whowechina/diva_pico/Production/CAD/diva_pico_base.stl

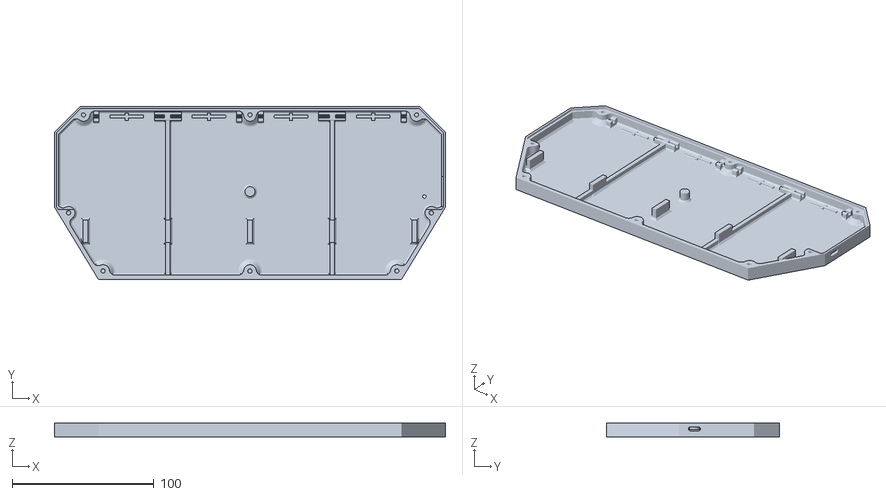
[picture p27: CAD file, 2025-04-21]
Production/CAD/diva_pico_base.stl
276.0 x 122.0 x 10.0
