whowechina/diva_pico/PCB/plus/3dmodels/SW_Kailh_Choc_V1.stp

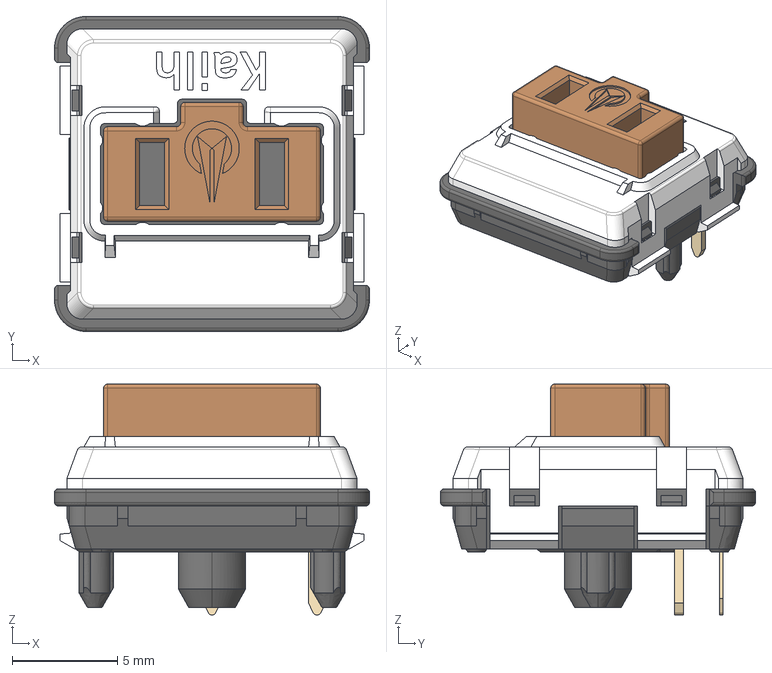
[picture p28: CAD file, 2023-12-16]
PCB/plus/3dmodels/SW_Kailh_Choc_V1.stp
15.0 x 15.0 x 11.0 mm
