whowechina/diva_pico/PCB/plus/3dmodels/WS2812B.step

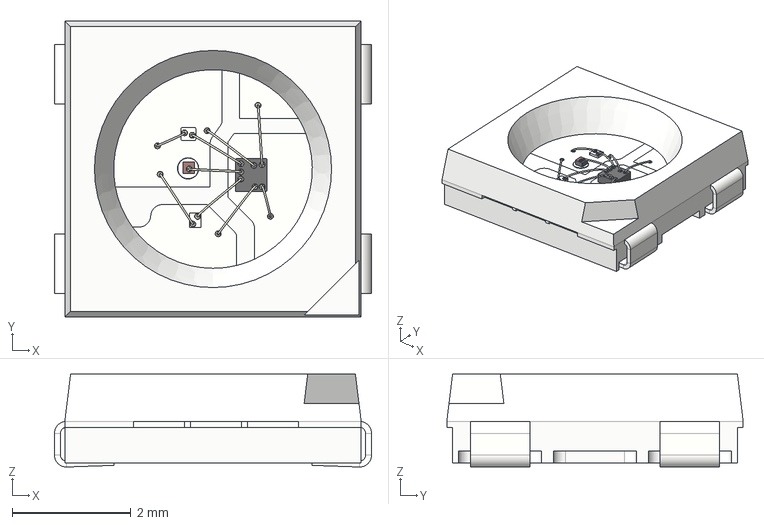
[picture p29: CAD file, 2023-12-16]
PCB/plus/3dmodels/WS2812B.step
5.35 x 5.00 x 1.57 mm
