whowechina/diva_pico/PCB/plus/3dmodels/chu_keypad_lgp.step

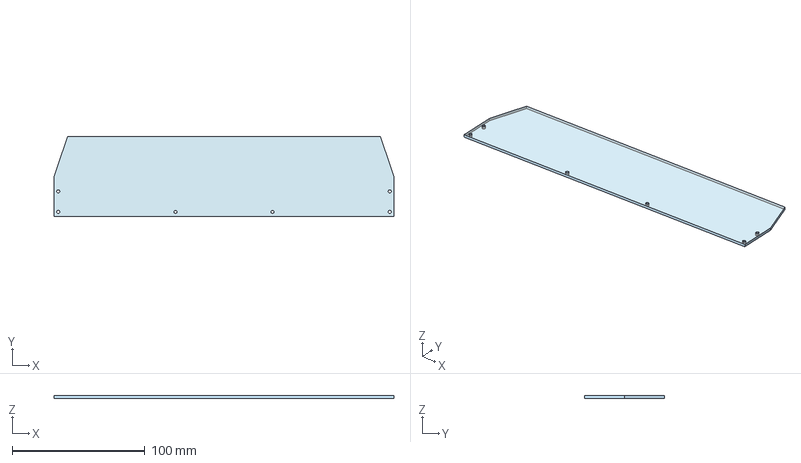
[picture p31: CAD file, 2023-12-16]
PCB/plus/3dmodels/chu_keypad_lgp.step
256.0 x 60.0 x 2.00 mm
