whowechina/diva_pico/PCB/plus/3dmodels/WS2812-2020.STEP

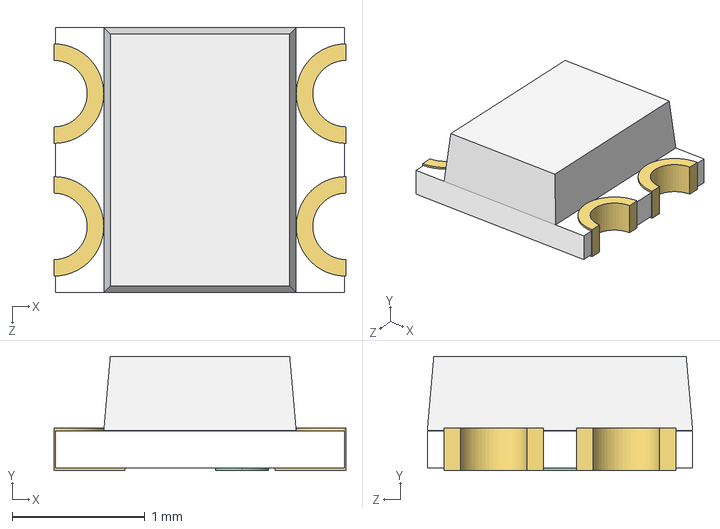
[picture p32: CAD file, 2023-12-16]
PCB/plus/3dmodels/WS2812-2020.STEP
2.20 x 0.86 x 2.00 mm
