whowechina/diva_pico/PCB/plus/3dmodels/J 2835.step

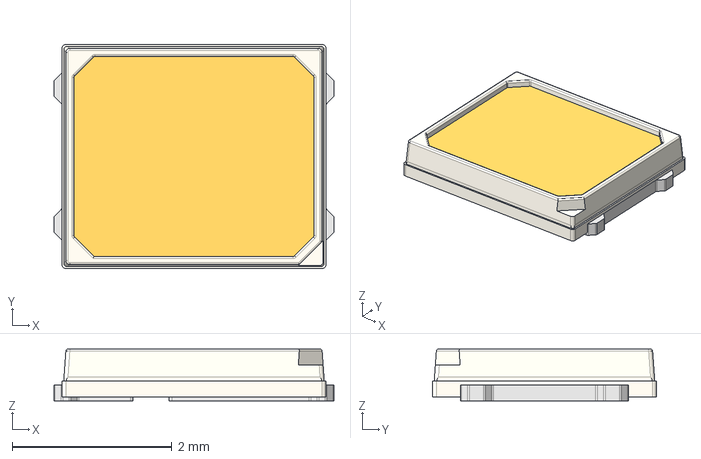
[picture p33: CAD file, 2023-12-16]
PCB/plus/3dmodels/J 2835.step
3.50 x 2.80 x 0.65 mm
