whowechina/diva_pico/PCB/plus/3dmodels/WS2812-0807.STEP

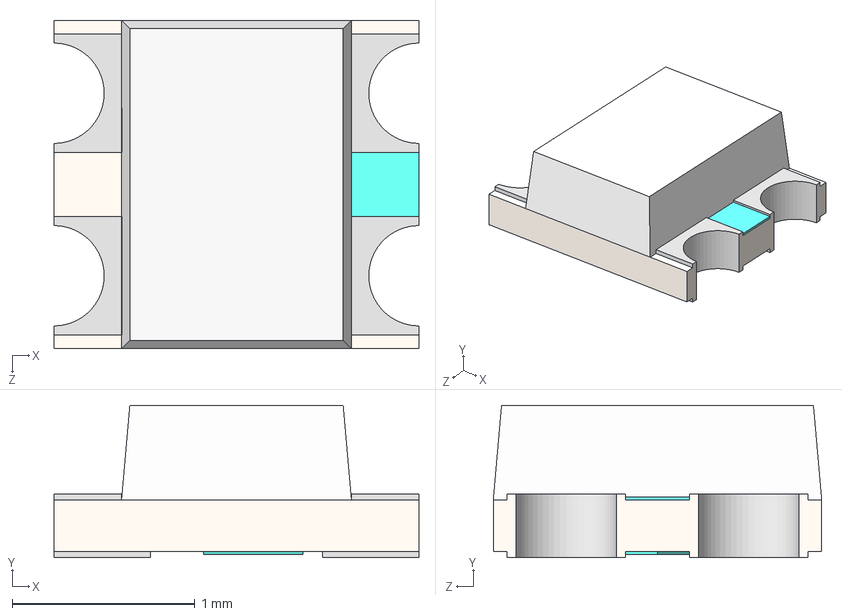
[picture p34: CAD file, 2023-12-16]
PCB/plus/3dmodels/WS2812-0807.STEP
2.00 x 0.835 x 1.80 mm
