whowechina/diva_pico/PCB/plus/3dmodels/Kailh LP Choc PC Keycap.step

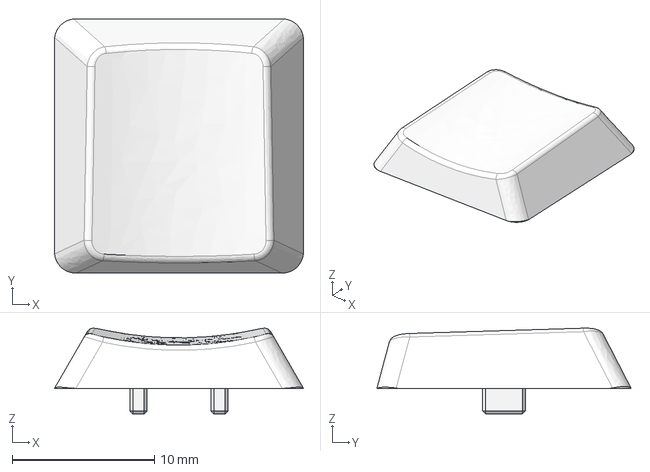
[picture p35: CAD file, 2023-12-16]
PCB/plus/3dmodels/Kailh LP Choc PC Keycap.step
17.5 x 17.9 x 6.03 mm
