whowechina/diva_pico/PCB/plus/3dmodels/SW_Hotswap_Kailh_MX.stp

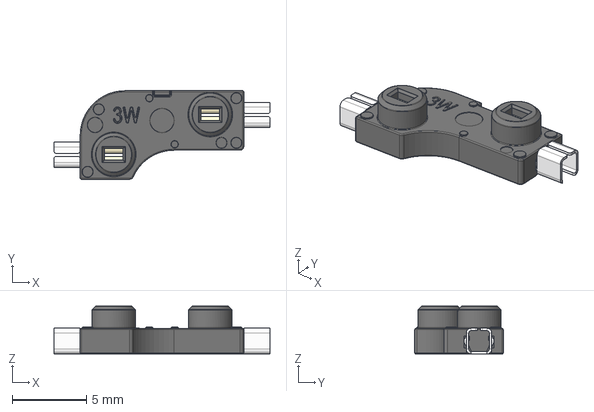
[picture p36: CAD file, 2023-12-16]
PCB/plus/3dmodels/SW_Hotswap_Kailh_MX.stp
14.5 x 5.95 x 3.22 mm
