whowechina/diva_pico/PCB/plus/3dmodels/SKPMAM.STEP

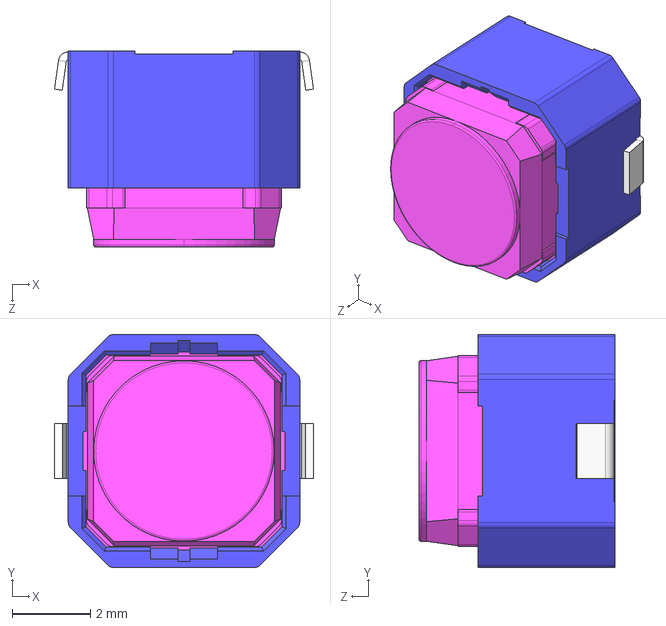
[picture p37: CAD file, 2023-12-16]
PCB/plus/3dmodels/SKPMAM.STEP
6.60 x 5.94 x 5.00 mm
