whowechina/diva_pico/PCB/plus/3dmodels/gp2y0e03.3mf

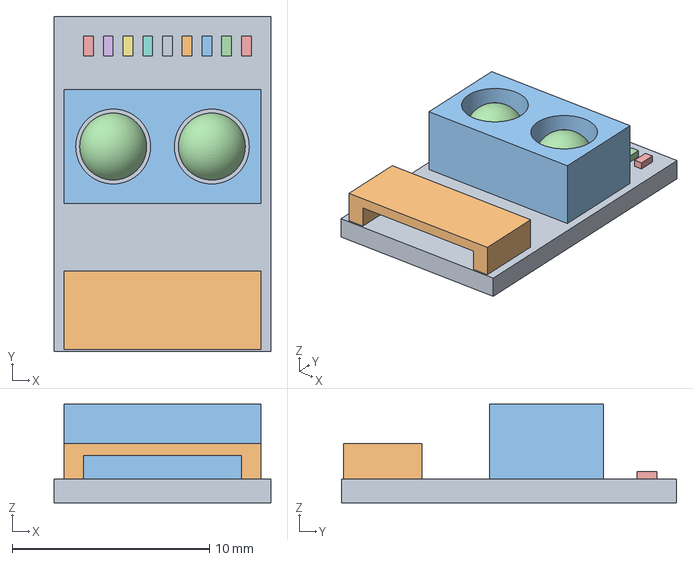
[picture p38: CAD file, 2023-12-16]
PCB/plus/3dmodels/gp2y0e03.3mf
11.0 x 17.0 x 5.00 mm
