whowechina/diva_pico/PCB/plus/3dmodels/Magnetic Pogo Connector 5 Pin (F).STEP

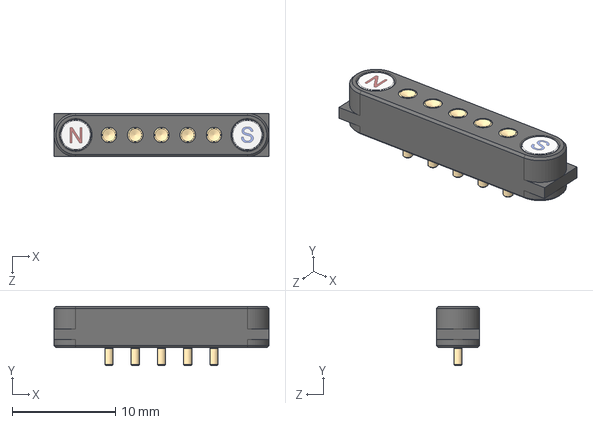
[picture p39: CAD file, 2023-12-16]
PCB/plus/3dmodels/Magnetic Pogo Connector 5 Pin (F).STEP
20.8 x 5.75 x 4.20 mm
