whowechina/diva_pico/PCB/plus/3dmodels/Tact Switch 4.5mm SMT.step

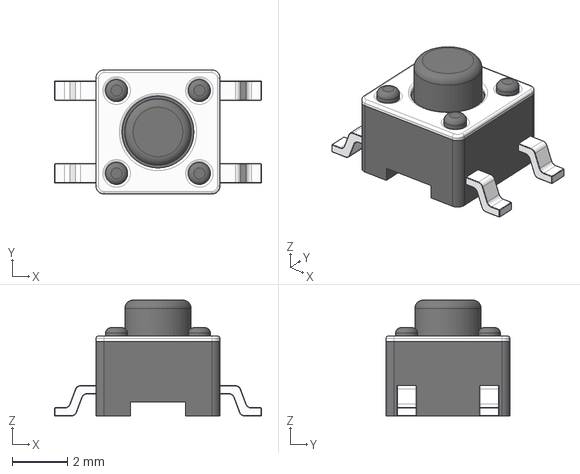
[picture p40: CAD file, 2023-12-16]
PCB/plus/3dmodels/Tact Switch 4.5mm SMT.step
7.50 x 4.50 x 4.20 mm
