whowechina/diva_pico/PCB/plus/3dmodels/User Library-WS2812-2020.step

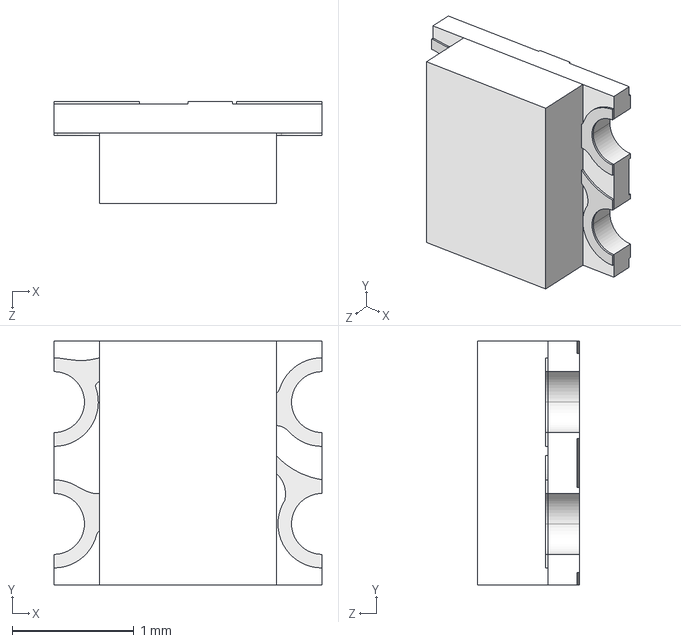
[picture p41: CAD file, 2023-12-16]
PCB/plus/3dmodels/User Library-WS2812-2020.step
2.20 x 2.00 x 0.84 mm
