whowechina/diva_pico/PCB/plus/3dmodels/EVQ-P1D05M.stp

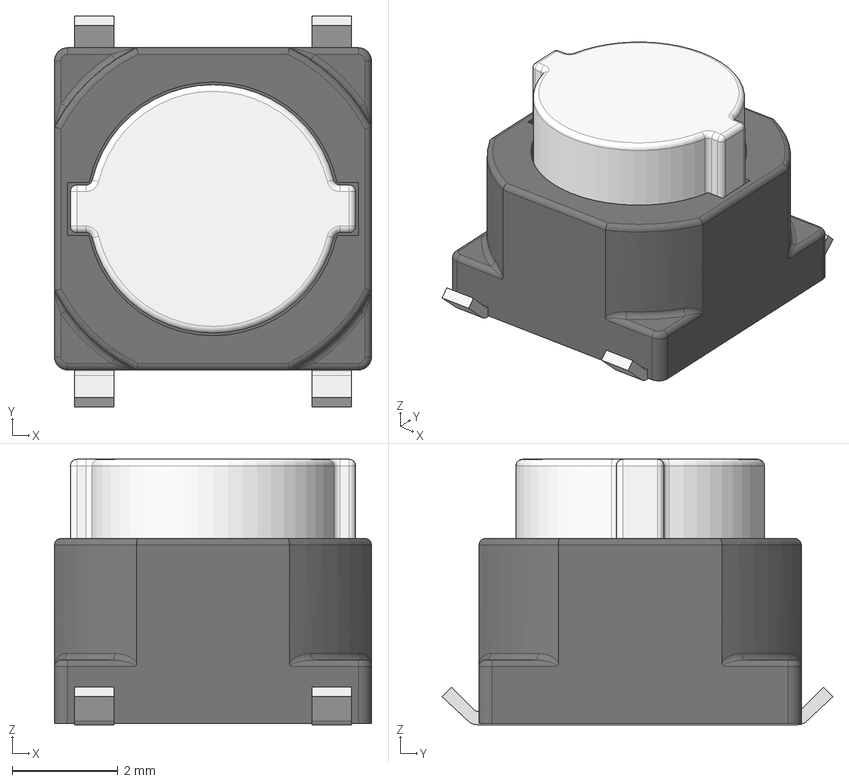
[picture p42: CAD file, 2023-12-16]
PCB/plus/3dmodels/EVQ-P1D05M.stp
6.00 x 7.40 x 5.03 mm
