whowechina/diva_pico/PCB/plus/3dmodels/Magnetic Pogo Connector 5 Pin (Type 4).STEP

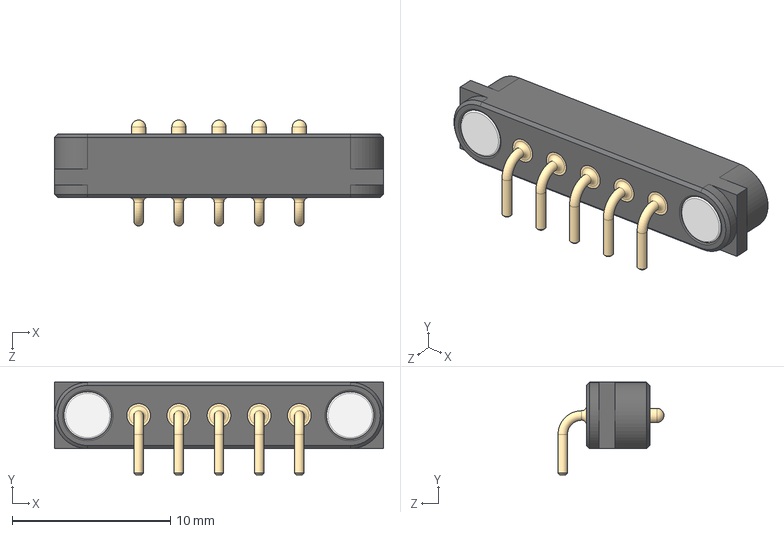
[picture p43: CAD file, 2023-12-16]
PCB/plus/3dmodels/Magnetic Pogo Connector 5 Pin (Type 4).STEP
20.8 x 5.85 x 6.70 mm
