whowechina/diva_pico/PCB/plus/3dmodels/User Library-WS2812-4020.step

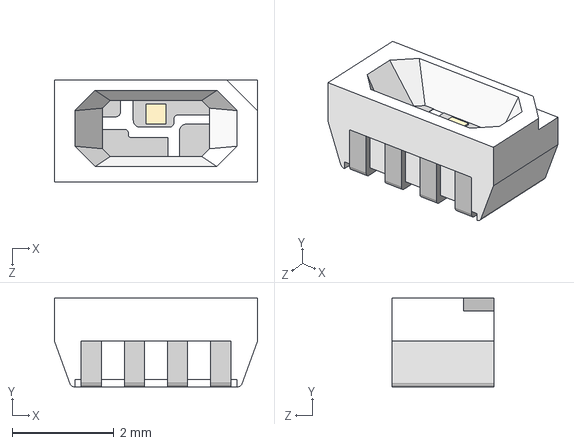
[picture p45: CAD file, 2023-12-16]
PCB/plus/3dmodels/User Library-WS2812-4020.step
4.00 x 1.75 x 2.00 mm
