whowechina/diva_pico/PCB/plus/3dmodels/User Library-PTS645SL95SMTR92-LFS.STEP

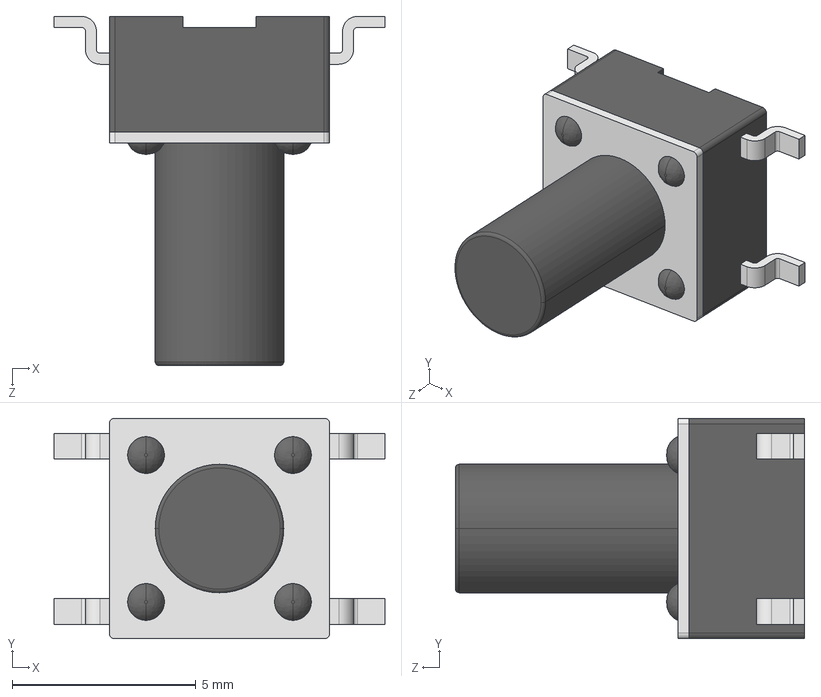
[picture p46: CAD file, 2023-12-16]
PCB/plus/3dmodels/User Library-PTS645SL95SMTR92-LFS.STEP
9.00 x 6.00 x 9.50 mm
