whowechina/diva_pico/firmware/src/mbedtls_config.h

/* This can be enabled lated when we use SNTP */
#undef MBEDTLS_HAVE_TIME_DATE

#define MBEDTLS_CHECK_PARAMS_ASSERT
#define MBEDTLS_ENTROPY_HARDWARE_ALT
#define MBEDTLS_AES_ROM_TABLES
#define MBEDTLS_AES_FEWER_TABLES
#define MBEDTLS_CAMELLIA_SMALL_MEMORY
#define MBEDTLS_CHECK_RETURN_WARNING
#undef MBEDTLS_FS_IO
#define MBEDTLS_NO_PLATFORM_ENTROPY
#undef MBEDTLS_PSA_CRYPTO_CLIENT
#undef MBEDTLS_PSA_CRYPTO_DRIVERS
#define MBEDTLS_SHA256_C
#define MBEDTLS_RSA_C
#define MBEDTLS_X509_RSASSA_PSS_SUPPORT
#define MBEDTLS_PKCS1_V21
#define MBEDTLS_BIGNUM_C
#define MBEDTLS_MD_C
#define MBEDTLS_SSL_ASYNC_PRIVATE
#define MBEDTLS_SSL_VARIABLE_BUFFER_LENGTH
#undef MBEDTLS_USE_PSA_CRYPTO
#define MBEDTLS_OID_C
#define MBEDTLS_X509_CRT_PARSE_C
#define MBEDTLS_SSL_MAX_FRAGMENT_LENGTH
#define MBEDTLS_X509_USE_C
#define MBEDTLS_ASN1_PARSE_C
#define MBEDTLS_BASE64_C
#define MBEDTLS_PEM_PARSE_C
#define MBEDTLS_PEM_WRITE_C
#define MBEDTLS_PK_PARSE_C
#define MBEDTLS_PK_WRITE_C
#define MBEDTLS_PKCS1_PARSE_C
#define MBEDTLS_PK_C
#undef MBEDTLS_NET_C
#undef MBEDTLS_PSA_CRYPTO_STORAGE_C
#undef MBEDTLS_PSA_ITS_FILE_C
#undef MBEDTLS_TIMING_C
